computergui63/TS1526/Images/1526-1.jpg

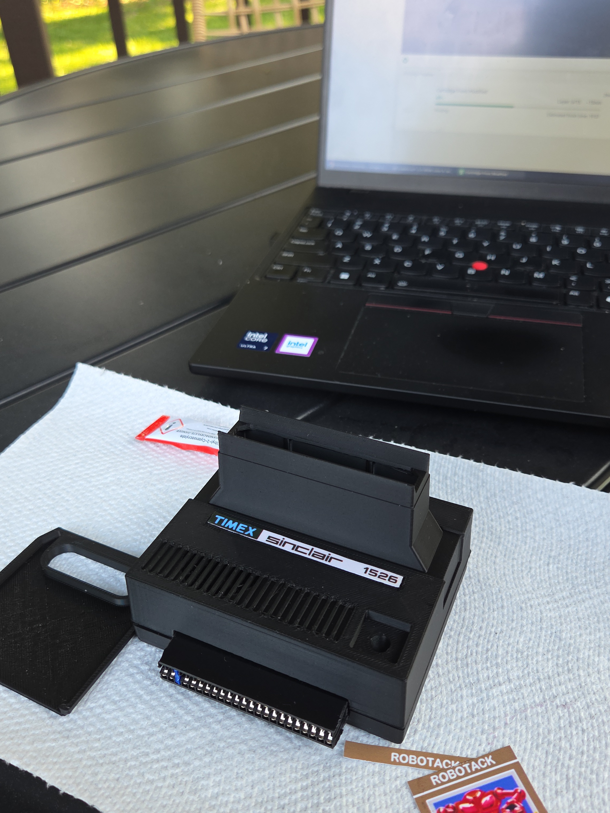
Images/1526-1.jpg
