computergui63/TS1526/Images/1526-2.jpg

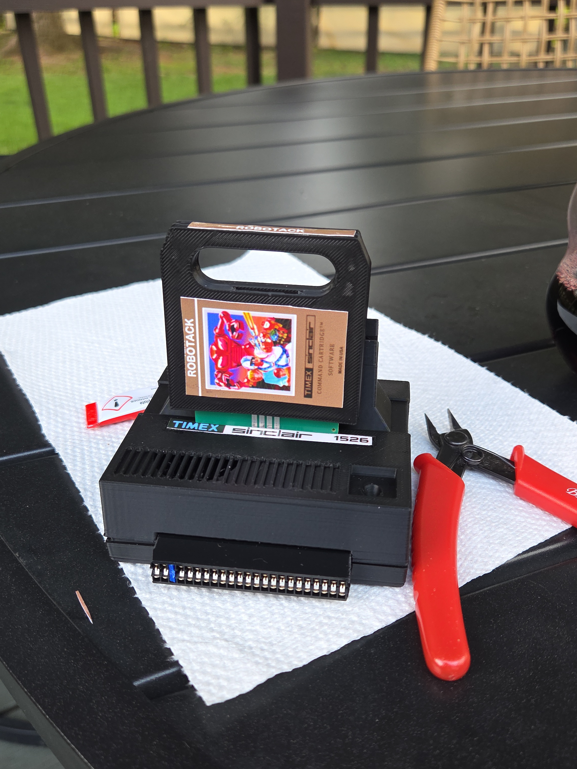
Images/1526-2.jpg
