computergui63/TS1526/Images/1526-3.jpg

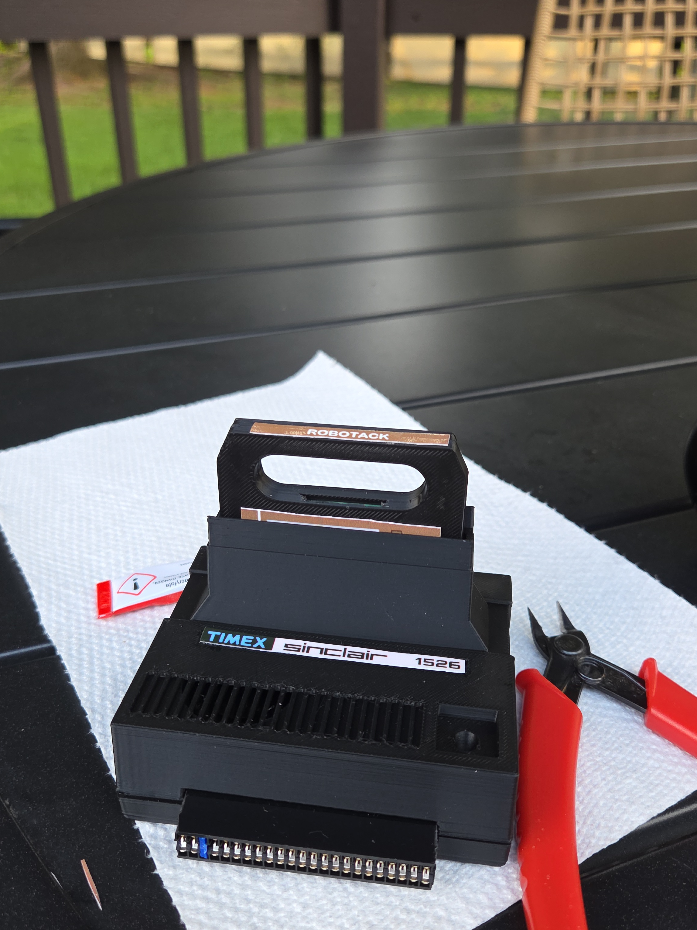
Images/1526-3.jpg
