computergui63/TS1526/Images/1526-5.png

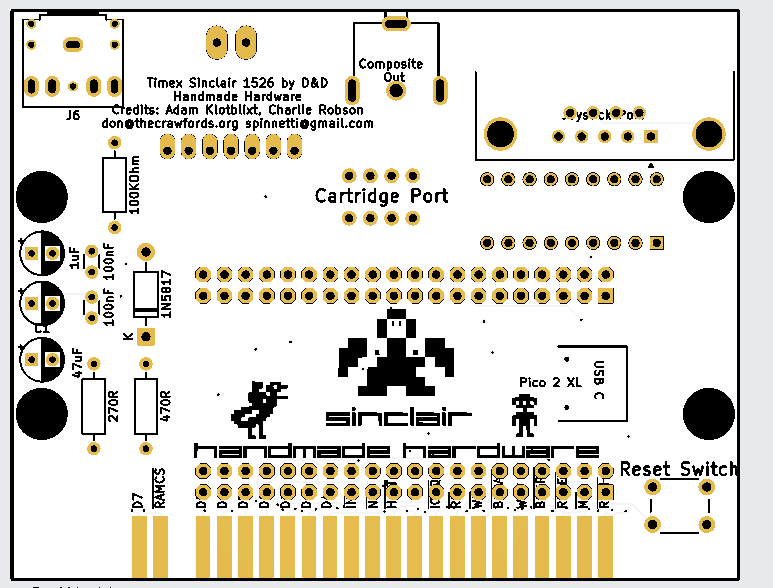
Images/1526-5.png
