computergui63/TS1526/Images/1526-7.jpg

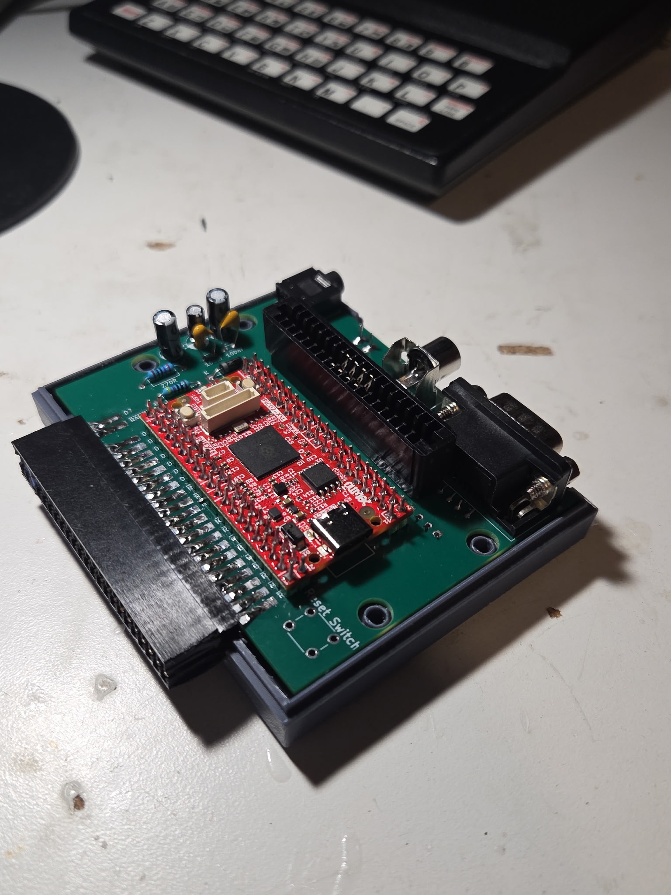
Images/1526-7.jpg
